tnl3pdx/SleepBud/Images/Sketches/L1 v2.png

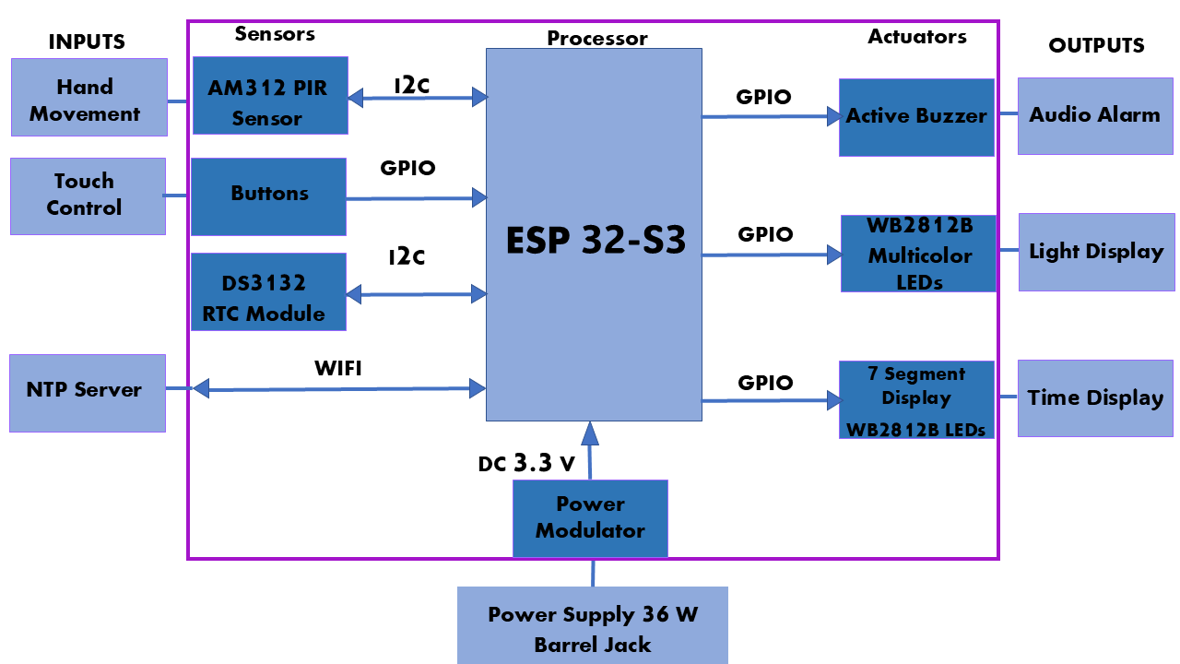
Images/Sketches/L1 v2.png
